EcutAtom336/AtomHeat/pic/AtomHeat_start.png

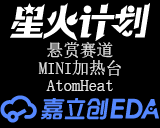
pic/AtomHeat_start.png
