EcutAtom336/AtomHeat/pic/IMG_20240809_100347.jpg

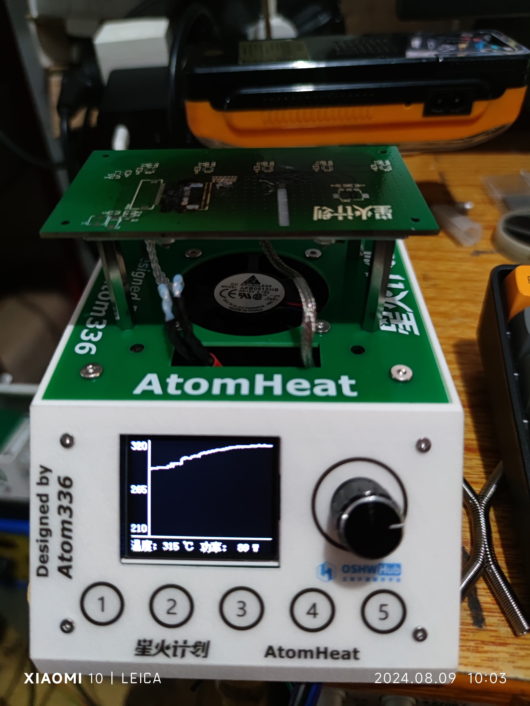
pic/IMG_20240809_100347.jpg
