EcutAtom336/AtomHeat/pic/IMG_20240809_143651.jpg

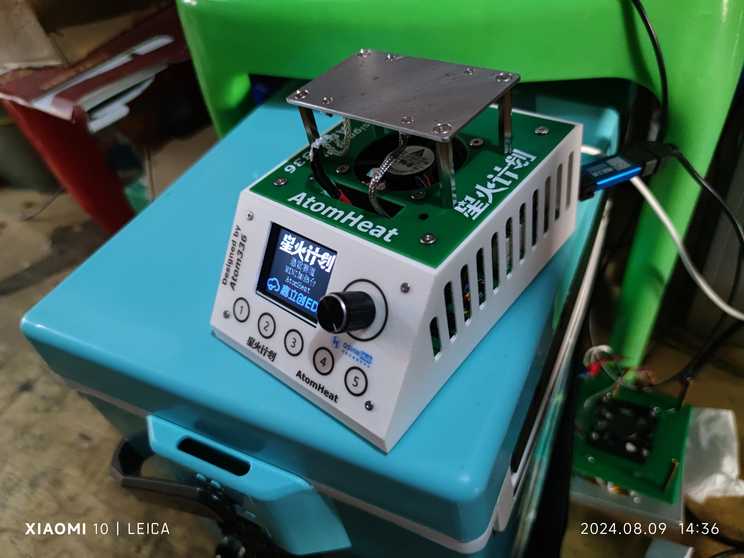
pic/IMG_20240809_143651.jpg
