EcutAtom336/AtomHeat/pic/IMG_20240809_143841.jpg

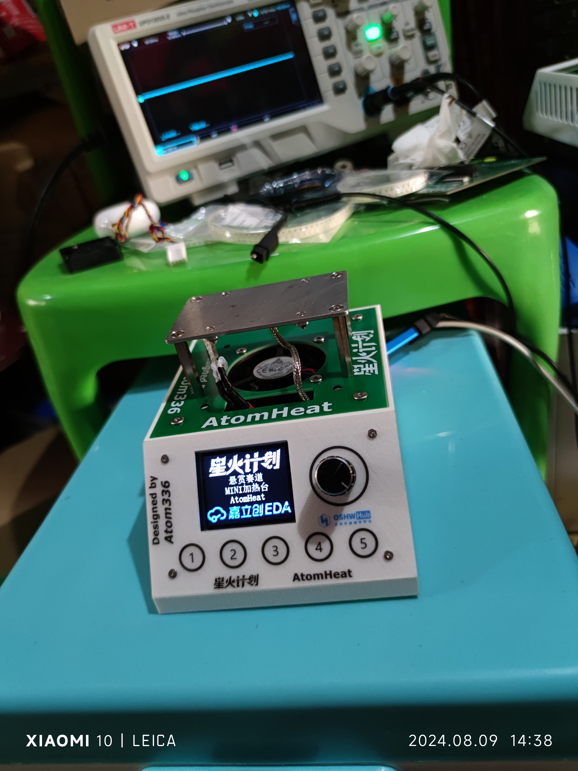
pic/IMG_20240809_143841.jpg
