EcutAtom336/AtomHeat/pic/耗材申请图片/屏幕截图(58).png

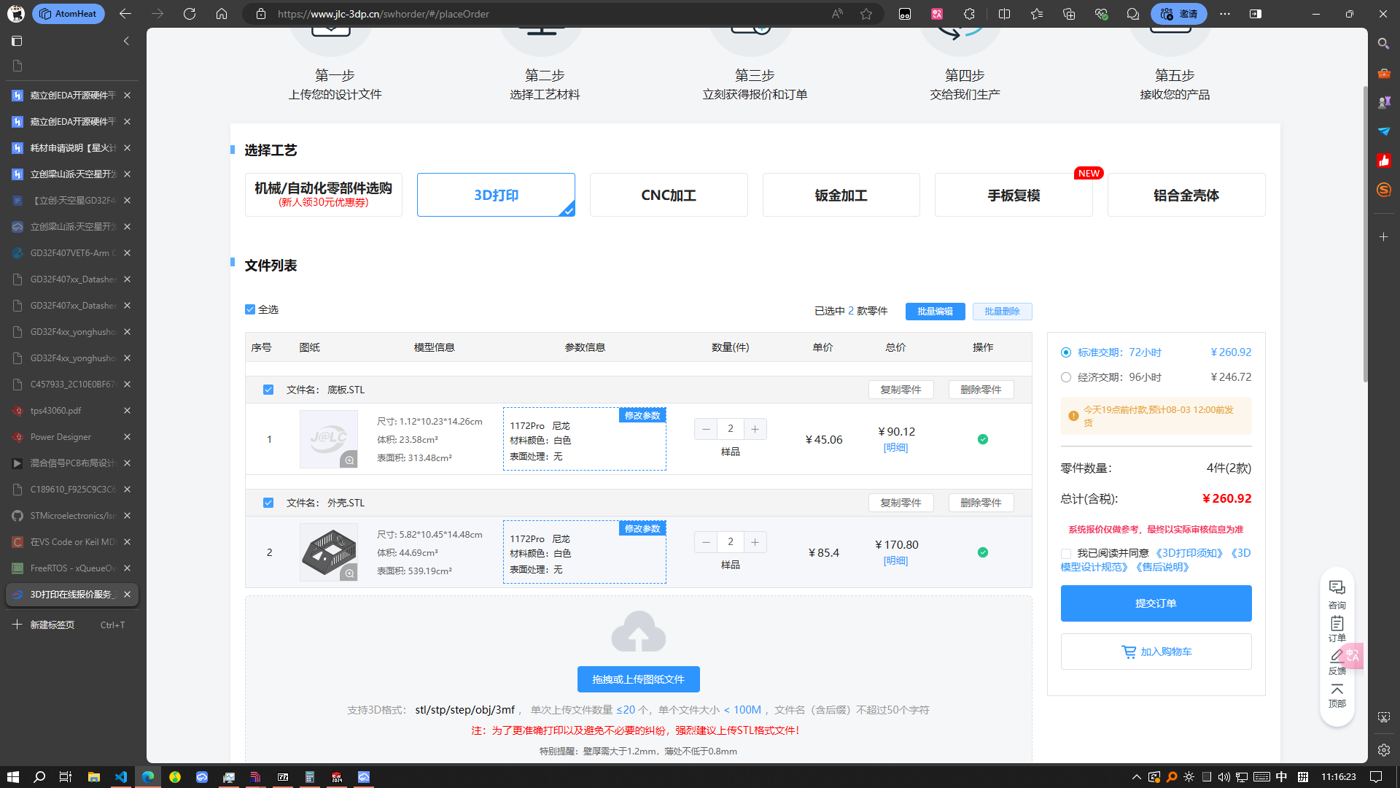
pic/耗材申请图片/屏幕截图(58).png
