EcutAtom336/AtomHeat/embed/AtomHeat/user/app/inc/set_heat_info_page.h

#ifndef _SET_HEAT_PROCEDURE_H_
#define _SET_HEAT_PROCEDURE_H_

/**
 * @brief 初始化设置加热参数界面
 * 
 */
void set_heat_info_page_init();

/**
 * @brief 启动设置加热参数界面
 * 
 */
void set_heat_info_page_start();

/**
 * @brief 停止设置加热参数界面
 * 
 */
void set_heat_info_page_stop();

#endif
