EcutAtom336/AtomHeat/embed/AtomHeat/user/gd32f4xx_it.c

/*!
    \file    gd32f4xx_it.c
    \brief   interrupt service routines

    \version 2024-01-15, V3.2.0, firmware for GD32F4xx
*/

/*
    Copyright (c) 2024, GigaDevice Semiconductor Inc.

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
    1. Redistributions of source code must retain the above copyright notice,
this list of conditions and the following disclaimer.
    2. Redistributions in binary form must reproduce the above copyright notice,
       this list of conditions and the following disclaimer in the documentation
       and/or other materials provided with the distribution.
    3. Neither the name of the copyright holder nor the names of its
contributors may be used to endorse or promote products derived from this
software without specific prior written permission.

    THIS SOFTWARE IS PROVIDED BY THE COPYRIGHT HOLDERS AND CONTRIBUTORS "AS IS"
AND ANY EXPRESS OR IMPLIED WARRANTIES, INCLUDING, BUT NOT LIMITED TO, THE
IMPLIED WARRANTIES OF MERCHANTABILITY AND FITNESS FOR A PARTICULAR PURPOSE ARE
DISCLAIMED. IN NO EVENT SHALL THE COPYRIGHT HOLDER OR CONTRIBUTORS BE LIABLE FOR
ANY DIRECT, INDIRECT, INCIDENTAL, SPECIAL, EXEMPLARY, OR CONSEQUENTIAL DAMAGES
(INCLUDING, BUT NOT LIMITED TO, PROCUREMENT OF SUBSTITUTE GOODS OR SERVICES;
LOSS OF USE, DATA, OR PROFITS; OR BUSINESS INTERRUPTION) HOWEVER CAUSED AND ON
ANY THEORY OF LIABILITY, WHETHER IN CONTRACT, STRICT LIABILITY, OR TORT
(INCLUDING NEGLIGENCE OR OTHERWISE) ARISING IN ANY WAY OUT OF THE USE OF THIS
SOFTWARE, EVEN IF ADVISED OF THE POSSIBILITY OF SUCH DAMAGE.
*/

#include "FreeRTOS.h"
//
#include "gd32f4xx_it.h"
#include "systick.h"

/*!
    \brief      this function handles NMI exception
    \param[in]  none
    \param[out] none
    \retval     none
*/
void NMI_Handler(void) {
  /* if NMI exception occurs, go to infinite loop */
  while (1) {
  }
}

/*!
    \brief      this function handles HardFault exception
    \param[in]  none
    \param[out] none
    \retval     none
*/
void HardFault_Handler(void) {
  /* if Hard Fault exception occurs, go to infinite loop */
  while (1) {
  }
}

/*!
    \brief      this function handles MemManage exception
    \param[in]  none
    \param[out] none
    \retval     none
*/
void MemManage_Handler(void) {
  /* if Memory Manage exception occurs, go to infinite loop */
  while (1) {
  }
}

/*!
    \brief      this function handles BusFault exception
    \param[in]  none
    \param[out] none
    \retval     none
*/
void BusFault_Handler(void) {
  /* if Bus Fault exception occurs, go to infinite loop */
  while (1) {
  }
}

/*!
    \brief      this function handles UsageFault exception
    \param[in]  none
    \param[out] none
    \retval     none
*/
void UsageFault_Handler(void) {
  /* if Usage Fault exception occurs, go to infinite loop */
  while (1) {
  }
}

/*!
    \brief      this function handles SVC exception
    \param[in]  none
    \param[out] none
    \retval     none
*/
// void SVC_Handler(void) {
//   vPortSVCHandler();
//   //   while (1);
// }

/*!
    \brief      this function handles DebugMon exception
    \param[in]  none
    \param[out] none
    \retval     none
*/
void DebugMon_Handler(void) {
  /* if DebugMon exception occurs, go to infinite loop */
  while (1) {
  }
}

/*!
    \brief      this function handles PendSV exception
    \param[in]  none
    \param[out] none
    \retval     none
*/
// void PendSV_Handler(void) {
//   xPortPendSVHandler();
//   //   while (1);
// }

/*!
    \brief    this function handles SysTick exception
    \param[in]  none
    \param[out] none
    \retval     none
*/
// void SysTick_Handler(void) {

// #if (INCLUDE_xTaskGetSchedulerState == 1)
//   if (xTaskGetSchedulerState() != taskSCHEDULER_NOT_STARTED) {
// #endif

//     xPortSysTickHandler();
// #if (INCLUDE_xTaskGetSchedulerState == 1)
//   }
// #endif
//   delay_decrement();
// }
