EcutAtom336/AtomHeat/embed/AtomHeat/user/utilities/util_flash.c

#include "util_flash.h"
//
#include "gd32f4xx.h"
//

uint32_t util_flash_get_sector_header_by_addr(uint32_t addr) {
  if (addr >= ADDR_FLASH_SECTOR_0 && addr < ADDR_FLASH_SECTOR_1)
    return ADDR_FLASH_SECTOR_0;
  else if (addr >= ADDR_FLASH_SECTOR_1 && addr < ADDR_FLASH_SECTOR_2)
    return ADDR_FLASH_SECTOR_1;
  else if (addr >= ADDR_FLASH_SECTOR_2 && addr < ADDR_FLASH_SECTOR_3)
    return ADDR_FLASH_SECTOR_2;
  else if (addr >= ADDR_FLASH_SECTOR_3 && addr < ADDR_FLASH_SECTOR_4)
    return ADDR_FLASH_SECTOR_3;
  else if (addr >= ADDR_FLASH_SECTOR_4 && addr < ADDR_FLASH_SECTOR_5)
    return ADDR_FLASH_SECTOR_4;
  else if (addr >= ADDR_FLASH_SECTOR_5 && addr < ADDR_FLASH_SECTOR_6)
    return ADDR_FLASH_SECTOR_5;
  else if (addr >= ADDR_FLASH_SECTOR_6 && addr < ADDR_FLASH_SECTOR_7)
    return ADDR_FLASH_SECTOR_6;
  else if (addr >= ADDR_FLASH_SECTOR_7 && addr < ADDR_FLASH_SECTOR_8)
    return ADDR_FLASH_SECTOR_7;
  else if (addr >= ADDR_FLASH_SECTOR_8 && addr < ADDR_FLASH_SECTOR_9)
    return ADDR_FLASH_SECTOR_8;
  else if (addr >= ADDR_FLASH_SECTOR_9 && addr < ADDR_FLASH_SECTOR_10)
    return ADDR_FLASH_SECTOR_9;
  else if (addr >= ADDR_FLASH_SECTOR_10 && addr < ADDR_FLASH_SECTOR_11)
    return ADDR_FLASH_SECTOR_10;
  else if (addr >= ADDR_FLASH_SECTOR_11 && addr < ADDR_FLASH_SECTOR_12)
    return ADDR_FLASH_SECTOR_11;
  else if (addr >= ADDR_FLASH_SECTOR_12 && addr < ADDR_FLASH_SECTOR_13)
    return ADDR_FLASH_SECTOR_12;
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
      break;
    case FlashSector17:
      fs = fmc_sector_erase(CTL_SECTOR_NUMBER_17);
      break;
    case FlashSector18:
      fs = fmc_sector_erase(CTL_SECTOR_NUMBER_18);
      break;
    case FlashSector19:
      fs = fmc_sector_erase(CTL_SECTOR_NUMBER_19);
      break;
    case FlashSector20:
      fs = fmc_sector_erase(CTL_SECTOR_NUMBER_20);
      break;
    case FlashSector21:
      fs = fmc_sector_erase(CTL_SECTOR_NUMBER_21);
      break;
    case FlashSector22:
      fs = fmc_sector_erase(CTL_SECTOR_NUMBER_22);
      break;
    case FlashSector23:
      fs = fmc_sector_erase(CTL_SECTOR_NUMBER_23);
      break;
    case FlashSector24:
      fs = fmc_sector_erase(CTL_SECTOR_NUMBER_24);
      break;
    case FlashSector25:
      fs = fmc_sector_erase(CTL_SECTOR_NUMBER_25);
      break;
    case FlashSector26:
      fs = fmc_sector_erase(CTL_SECTOR_NUMBER_26);
      break;
    case FlashSector27:
      fs = fmc_sector_erase(CTL_SECTOR_NUMBER_27);
      break;
    default:
      break;
  }
  return fs;
}
